HyperPROBELabs/cyberdeck-hw/main/screen-panel/mechanical/panel/production/mesh-3d-printing/rod-holder.stl

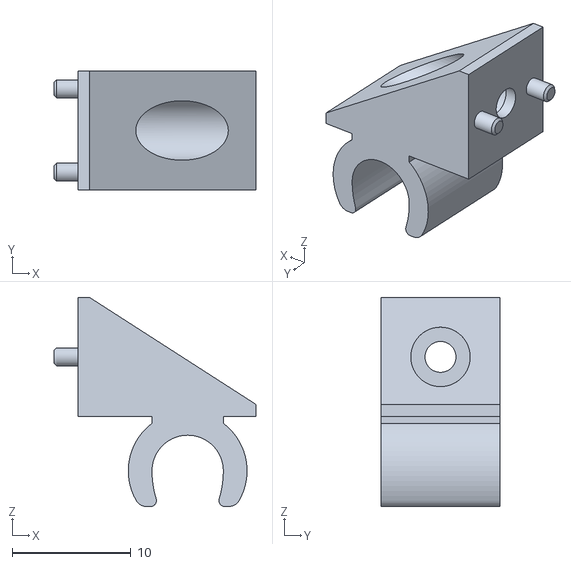
[picture p17: CAD file, 2026-04-27]
main/screen-panel/mechanical/panel/production/mesh-3d-printing/rod-holder.stl
17.0 x 10.0 x 17.6
