HyperPROBELabs/cyberdeck-hw/main/screen-panel/mechanical/panel/production/parts/screen-plate.step

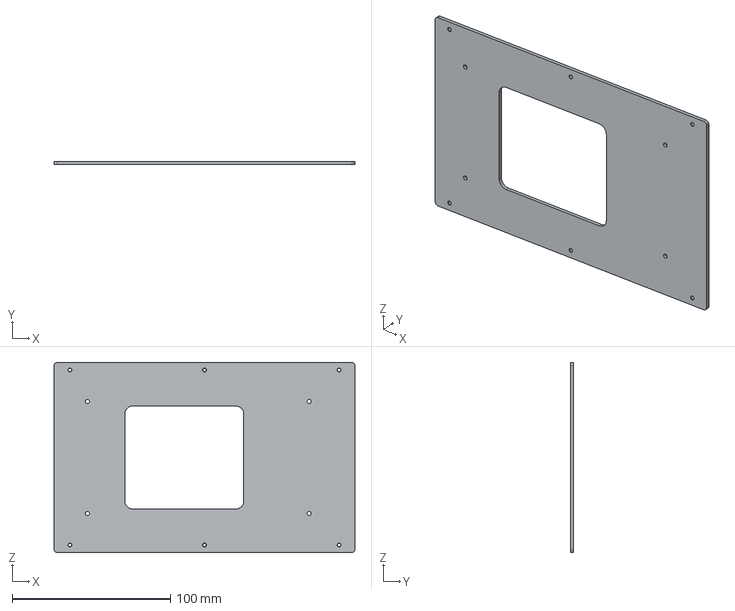
[picture p18: CAD file, 2026-04-27]
main/screen-panel/mechanical/panel/production/parts/screen-plate.step
190.0 x 2.00 x 120.0 mm
