HyperPROBELabs/cyberdeck-hw/main/screen-panel/mechanical/rod/production/mesh-3d-printing/rod-latch.stl

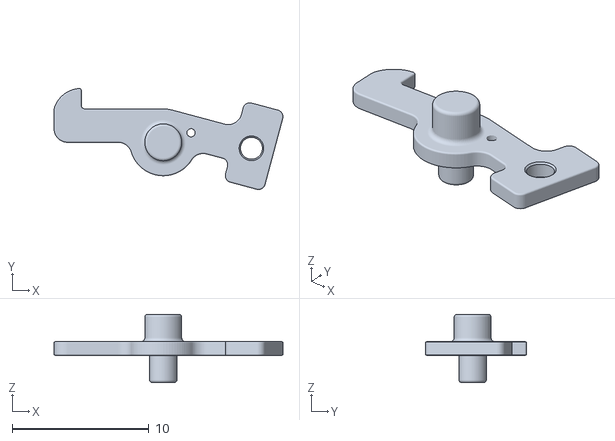
[picture p19: CAD file, 2026-04-22]
main/screen-panel/mechanical/rod/production/mesh-3d-printing/rod-latch.stl
16.8 x 7.40 x 5.00
