HyperPROBELabs/cyberdeck-hw/main/screen-panel/mechanical/panel/production/parts/screen-tpu.step

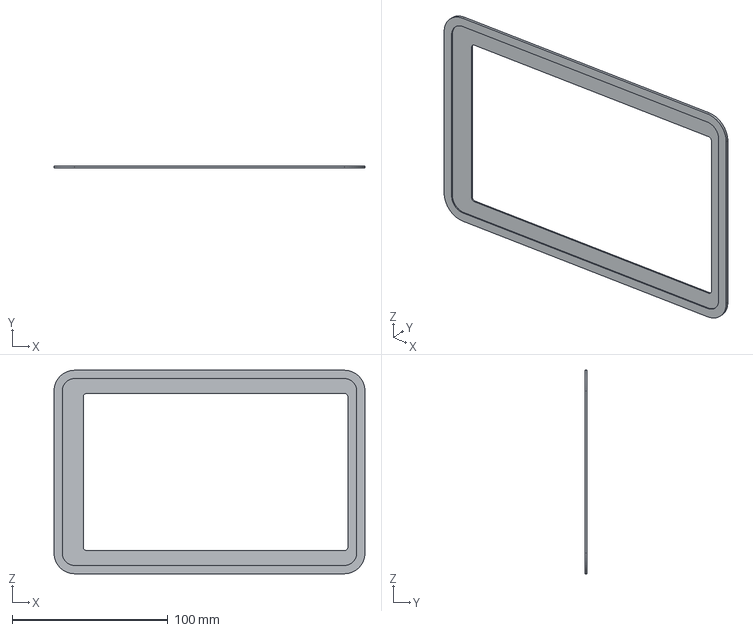
[picture p20: CAD file, 2026-04-27]
main/screen-panel/mechanical/panel/production/parts/screen-tpu.step
200.0 x 1.50 x 130.9 mm
