HyperPROBELabs/cyberdeck-hw/main/screen-panel/mechanical/panel/production/mesh-3d-printing/screen-base-frame.stl

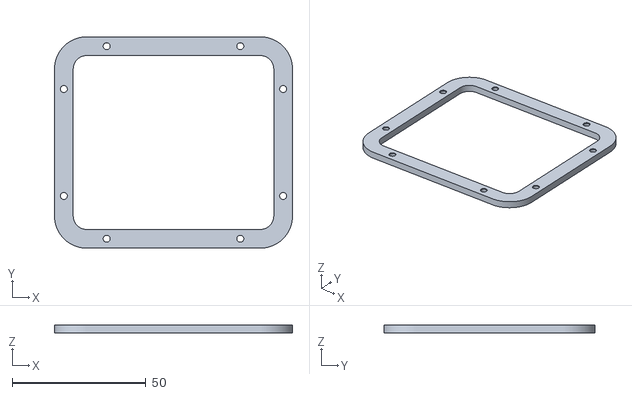
[picture p21: CAD file, 2026-04-27]
main/screen-panel/mechanical/panel/production/mesh-3d-printing/screen-base-frame.stl
89.0 x 79.0 x 3.00
