HyperPROBELabs/cyberdeck-hw/main/screen-panel/mechanical/panel/production/parts/rod-base.step

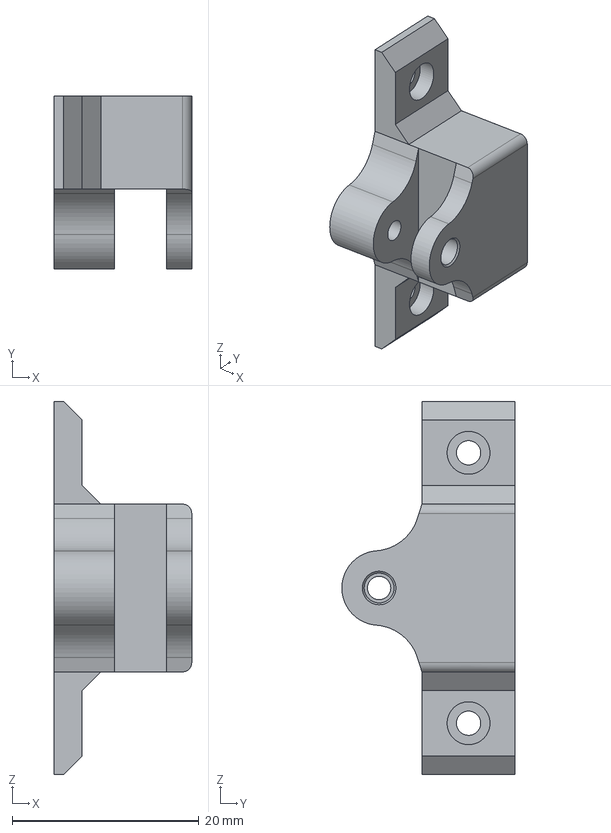
[picture p22: CAD file, 2026-04-27]
main/screen-panel/mechanical/panel/production/parts/rod-base.step
14.8 x 18.6 x 40.0 mm
