HyperPROBELabs/cyberdeck-hw/main/screen-panel/mechanical/panel/production/mesh-3d-printing/screen-angle-bracket.stl

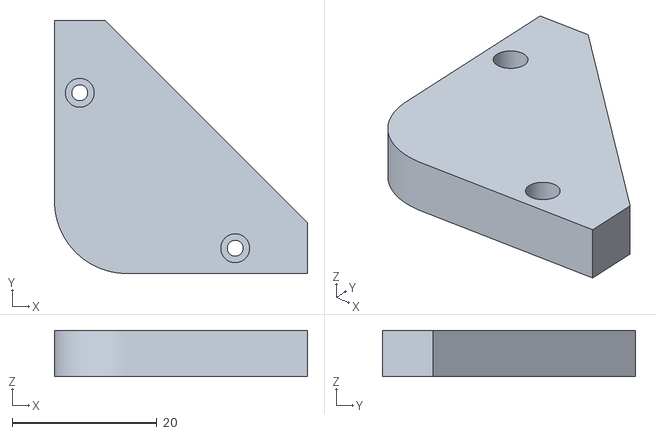
[picture p23: CAD file, 2026-04-27]
main/screen-panel/mechanical/panel/production/mesh-3d-printing/screen-angle-bracket.stl
35.0 x 35.0 x 6.40
